tloimu/ya-hotas-throttle/throttle-assembly.scad

include <throttle.scad>;

Throttle();

/*
TODO:

- kaapelireiän paikka koteloon (pieni reikä)
- kanteen detent-palikka ja sen kolo
- pohjan kannen pulttituet korkeammiksi

*/
